adoble/rusty-radio/software/controller/radio-control-protocol/src/lib.rs

#![cfg_attr(not(test), no_std)]

pub mod uart_handler;
pub use uart_handler::{UartHandler, UartHandlerError, command::Command};

pub mod radio_control_protocol;
pub use radio_control_protocol::RadioControlProtocol;
